WhelpImAGhost/LED20/Gantt Chart/LED20 Gantt Chart v3.pdf

29 | 6 | 13 | 20 | 27 | 3 | 10 | 17 | 24 | 1 | 8
9/24 | 10/24 | 11/24 | 12/24
ECE 411 - LED20 Practicum ... | 0h | 100%
Assignments | 0h | 100%
Class Survey | 0 | 100%
Resume | 0 | 100%
Form Practicum Teams | 0 | 100%
Set up Collab Site | 0 | 100%
Generate 3 Projects and Choose 1 | 0 | 100%
Product Design Specification (PDS) | 0 | 100%
Preliminary Schematic | 0 | 100%
Decision Matrix and AHP | 0 | 100%
Project Schedule | 0 | 100%
Updated Schematic | 0 | 100%
Preliminary PCB Layout | 0 | 100%
Breadboard Prototype | 0 | 100%
Rough Draft of CAD | 0 | 100%
Functional Decomposition | 0 | 100%
Bill of Materials | 0 | 100%
Design Review | 0 | 100%
Final CAD | 0 | 100%
Send Board to Fab | 0 | 100%
Sign up for Practicum Demo | 0 | 100%
Test Plan | 0 | 100%
Practicum Demo | 0 | 100%
Assignments Complete! | 0 | 100%
Phase 1 - Concept Generation | 0h | 100%
Brainstorm Project Ideas | 0 | 100%
Product Design Specification (PDS) | 0 | 100%
Preliminary Schematic | 0 | 100%
Concept Complete! | 0 | 100%
Phase 2 - Prototype Development | 0h | 100%
Updated Schematic | 0 | 100%
Preliminary PCB Layout | 0 | 100%
Preliminary 3D Model - D20 | 0 | 100%
Set up ESP32 | 0 | 100%
Test ESP32 | 0 | 100%
Set up Gyroscope | 0 | 100%
Test Gyroscope | 0 | 100%
Set up Accelerometer | 0 | 100%
Test Accelerometer | 0 | 100%
Set up LEDs | 0 | 100%
Test Complete Prototype | 0 | 100%
Discuss Wireless Charging Options | 0 | 100%
Settle on Wireless or USB Charging | 0 | 100%
Prototype Complete! | 0 | 100%
Phase 3 - MVP Development | 0h | 100%
Final BOM | 0 | 100%
Updated 3D Model - PCB and Battery... | 0 | 100%
Integrate Wireless Charging | 0 | 100%
Final CAD | 0 | 100%
Final 3D Model - D20 Halves Locking... | 0 | 100%
Fully Integrate Programming | 0 | 100%
Fully Integrate All Components | 0 | 100%
Send Board to Fab | 0 | 100%
MVP Complete! | 0 | 100%
Phase 4 - Final Testing and Delivery | 0h | 100%
Pick up Board from EPL | 0 | 100%
Test Board | 0 | 100%
Write Presentation Slides | 0 | 100%
Practice Presentation and Demo | 0 | 100%
Present | 0 | 100%
Project Complete! | 0 | 100%

Brad Glaubitz, Caleb Monti, Chris Kane-Pardy, Henry Sanders
Brad Glaubitz, Caleb Monti, Chris Kane-Pardy, Henry Sanders Brad Glaubitz, Caleb Monti, Chris Kane-Pardy, Henry Sanders Caleb Monti
Chris Kane-Pardy, Henry Sanders
Brad Glaubitz, Caleb Monti, Chris Kane-Pardy, Henry Sanders Brad Glaubitz, Henry Sanders
Henry Sanders
Henry Sanders
Brad Glaubitz, Henry Sanders
Brad Glaubitz, Caleb Monti, Chris Kane-Pardy, Henry Sanders Caleb Monti, Chris Kane-Pardy
Brad Glaubitz, Caleb Monti, Chris Kane-Pardy, Henry Sanders Caleb Monti, Henry Sanders Brad Glaubitz
Brad Glaubitz, Caleb Monti, Chris Kane-Pardy, Henry Sanders
Brad Glaubitz, Caleb Monti, Chris Kane-Pardy, Henry Sanders
Brad Glaubitz, Caleb Monti, Chris Kane-Pardy, Henry Sanders Brad Glaubitz, Caleb Monti, Chris Kane-Pardy, Henry Sanders
Brad Glaubitz, Caleb Monti, Chris Kane-Pardy, Henry Sanders Brad Glaubitz, Caleb Monti, Chris Kane-Pardy, Henry Sanders

Brad Glaubitz, Caleb Monti, Chris Kane-Pardy, Henry Sanders
Brad Glaubitz, Caleb Monti, Chris Kane-Pardy, Henry Sanders Brad Glaubitz, Henry Sanders

Brad Glaubitz, Henry Sanders
Brad Glaubitz, Caleb Monti, Chris Kane-Pardy, Henry Sanders Chris Kane-Pardy
Caleb Monti
Caleb Monti
Caleb Monti
Caleb Monti
Caleb Monti
Caleb Monti
Caleb Monti
Brad Glaubitz, Caleb Monti, Chris Kane-Pardy, Henry Sanders Brad Glaubitz, Henry Sanders
Brad Glaubitz, Henry Sanders

Brad Glaubitz, Chris Kane-Pardy Chris Kane-Pardy
Brad Glaubitz, Henry Sanders
Brad Glaubitz, Caleb Monti, Chris Kane-Pardy, Henry Sanders Chris Kane-Pardy
Caleb Monti, Chris Kane-Pardy Brad Glaubitz, Chris Kane-Pardy, Henry Sanders Brad Glaubitz, Caleb Monti, Chris Kane-Pardy, Henry Sanders

Caleb Monti
Brad Glaubitz, Caleb Monti, Chris Kane-Pardy, Henry Sanders
Brad Glaubitz, Caleb Monti, Chris Kane-Pardy, Henry Sanders
Brad Glaubitz, Caleb Monti, Chris Kane-Pardy, Henry Sanders Brad Glaubitz, Caleb Monti, Chris Kane-Pardy, Henry Sanders

Powered by TCPDF (www.tcpdf.org)
