WhelpImAGhost/LED20/Functional Decomposition/Functional Decomposition.pdf

Caleb Monti
Brad Glaubitz
Henry Sanders
Chris Kane-Pardy
14 November 2024

## LED 20: Functional Decomposition

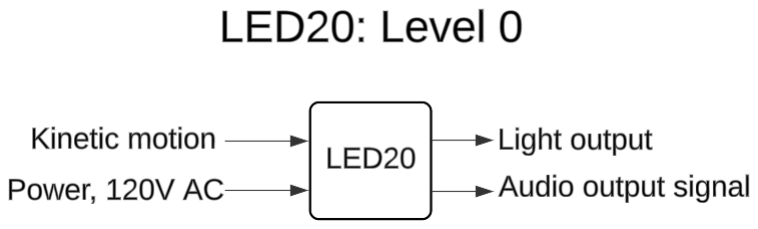
[picture p8: figure]

Module | LED20
Inputs | Kinetic motion: Significant motion detection Power: 120V AC rms, 60 Hz
Outputs | Light output: LEDs Audio output signal: Buzzer
Functionality | The device is interrupted via a significant motion from the user, producing light and audio outputs.

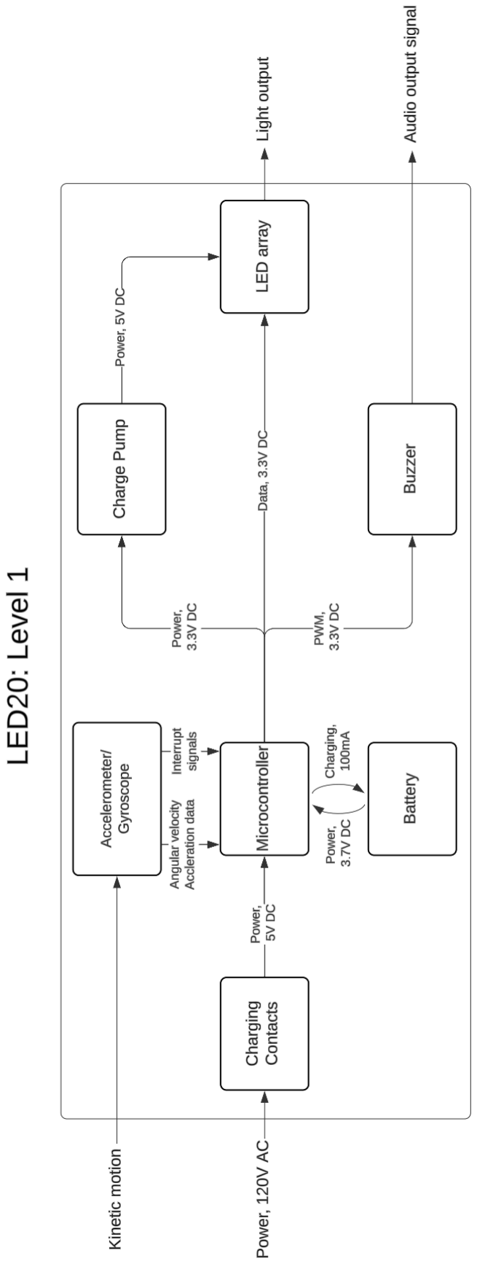
[picture p9: figure]

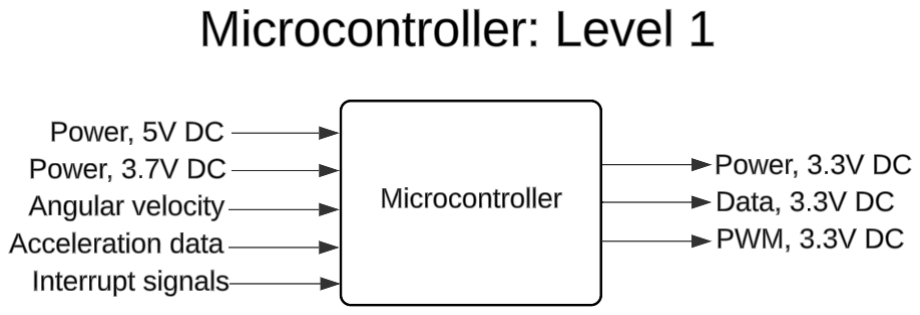
[picture p10: figure]

Module | Microcontroller
Inputs | Power: 5V DC from Charging Contacts Power: 3.7V DC from Battery Angular velocity: (-500, 500) degrees per second (DPS) Acceleration data: (0-4) g (acceleration due to gravity 2 g = 9. 81m/s ) Interrupt signals: to Accelerometer/Gyroscope
Outputs | Power: 3.3V DC to Charge Pump Data: 3.3V DC to LED array PWM: 3.3V DC to Buzzer
Functionality | Receives 5V DC from Charging Contacts for charging the battery, 3.7V DC from the battery to power self, angular velocity and acceleration data from Accelerometer/Gyroscope for determining when the device is in motion, no longer in motion, and at what orientation, and interrupt signals to Accelerometer/Gyroscope for both waking device up and putting to sleep after a period of unuse. Outputs 3.3V DC to charge pump, 3.3V data signal to LED Array based on angular velocity and acceleration data, and 3.3V PWM signal to Buzzer based on the orientation of the device.

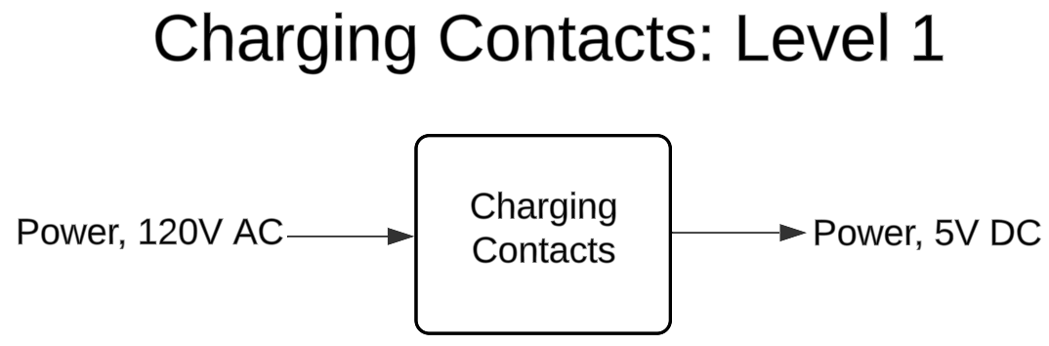
[picture p11: figure]

Module | Charging Contacts
Inputs | Power: 120V AC rms, 60 Hz
Outputs | Power: 5V DC
Functionality | Provide wireless charging via conductive contacts

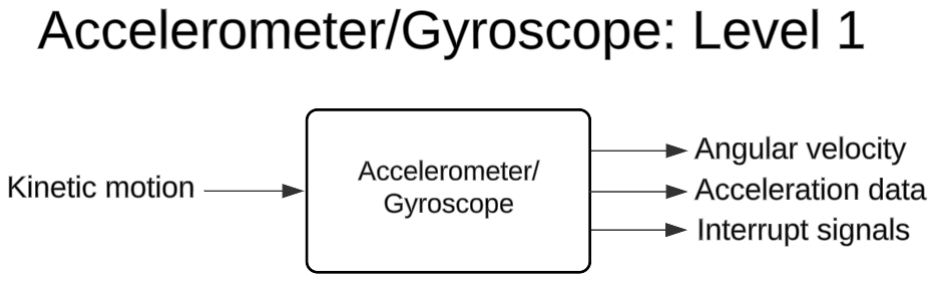
[picture p12: figure]

Module | Accelerometer/Gyroscope
Inputs | Kinetic motion: Significant motion detection
Outputs | Angular velocity: (-500, 500) dps Acceleration data: (0-4) g Interrupt signals: to Microcontroller
Functionality | Detects significant motion from the user, relays angular velocity and acceleration data to the Microcontroller, interrupt signals to both wake up and put the Accelerometer/Gyroscope to sleep.

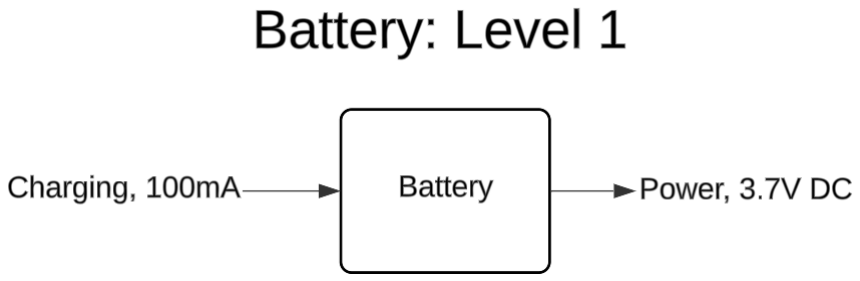
[picture p13: figure]

Module | Battery
Inputs | Charging: 100mA, limited by Microcontroller
Outputs | Power: 3.7V DC
Functionality | 500mAh LiPo battery, supplies 3.7V DC to Microcontroller

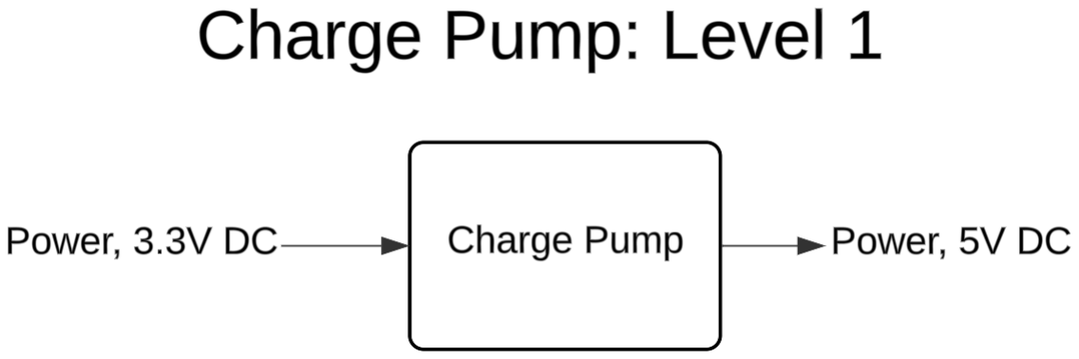
[picture p14: figure]

Module | Charge Pump
Inputs | Power: 3.3V DC from Microcontroller
Outputs | Power: 5V DC, 250mA max
Functionality | Converts 3.3V input from Microcontroller to 5V output to power LED Array

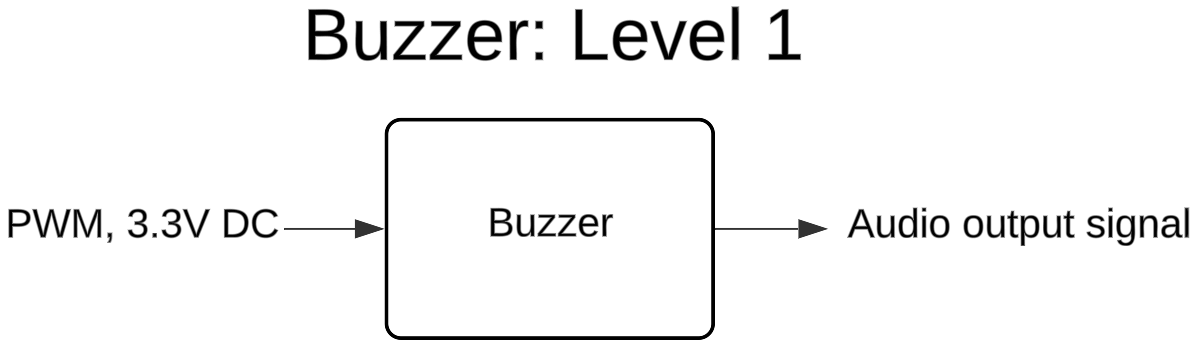
[picture p15: figure]

Module | Buzzer
Inputs | PWM: 3.3V DC
Outputs | Audio output signal: celebratory or disheartening tune
Functionality | Receives 3.3V PWM signal from microcontroller when particular values are read from accelerometer/gyroscope, emits tune based on the read value

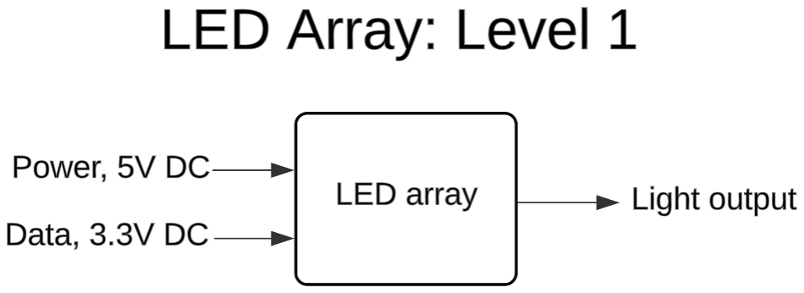
[picture p16: figure]

Module | LED Array
Inputs | Power: 5V DC from charge pump Data: 3.3V DC signal from microcontroller
Outputs | Light output: LEDs
Functionality | Illuminates particular LED in the array based on the orientation of the device determined by the accelerometer/gyroscope module
