WhelpImAGhost/LED20/CAD/Schematics and PCB Layouts/PDFs/Schematic/Updated Schematic 11-4-24/led20_updated_schematic_11_4_24.pdf

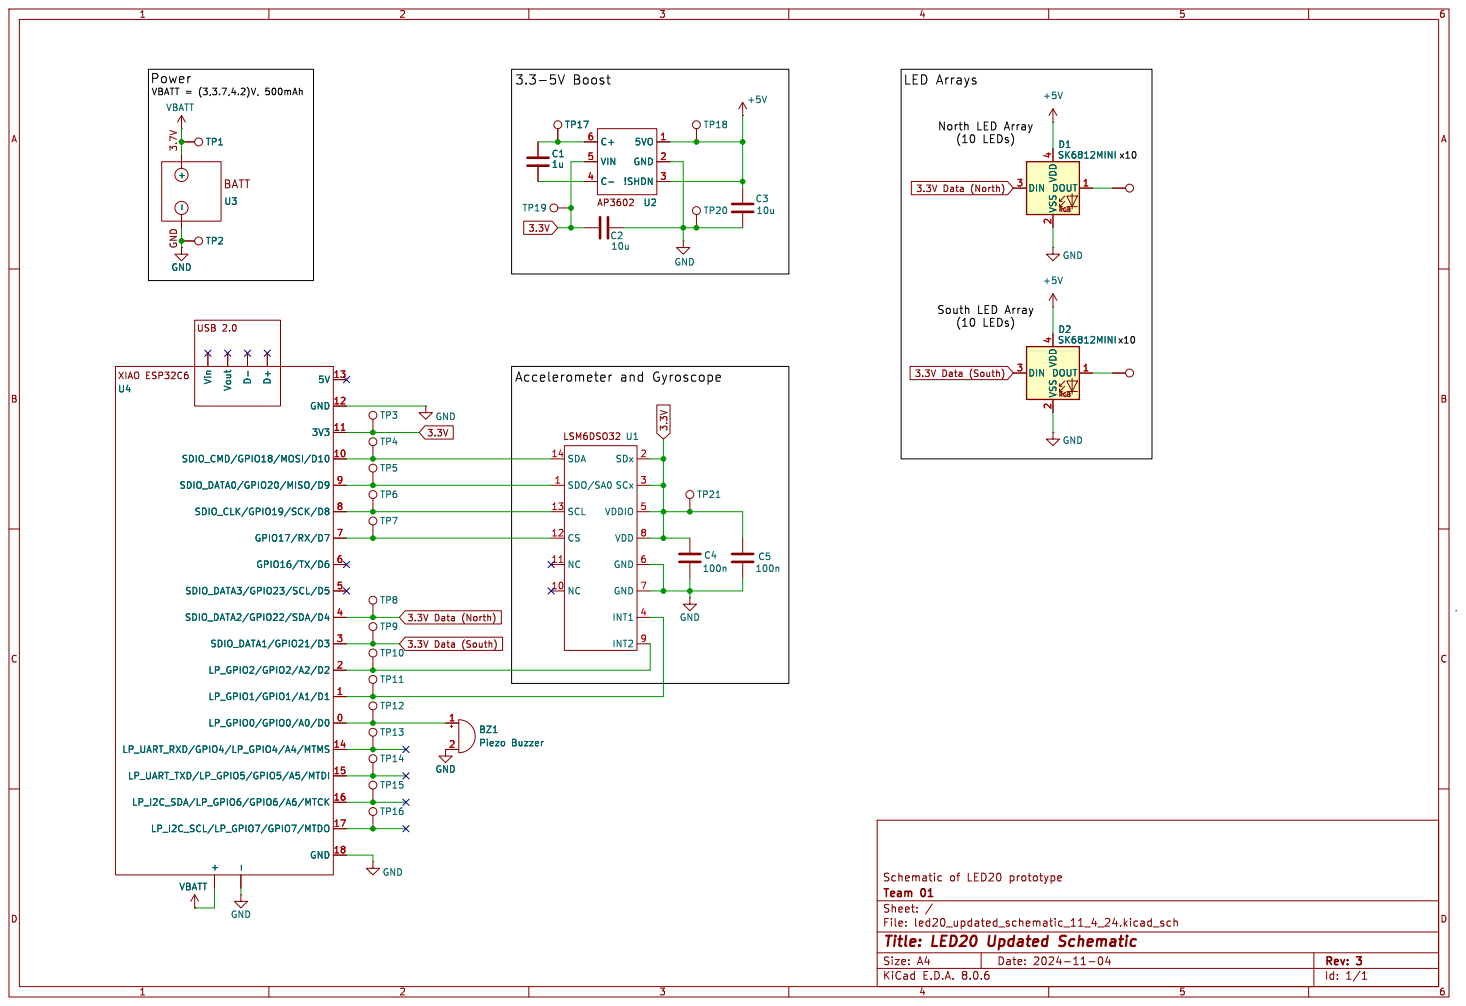
[picture p31: page 1]

x10 LED Arrays
(10 LEDs) North LED Array

3.3V Data (South)

Id: 1/1 Title: LED20 Updated Schematic
