WhelpImAGhost/LED20/CAD/Schematics and PCB Layouts/PDFs/Schematic/Updated Schematic 10-31-24/led20_updated_schematic_10_31_24.pdf

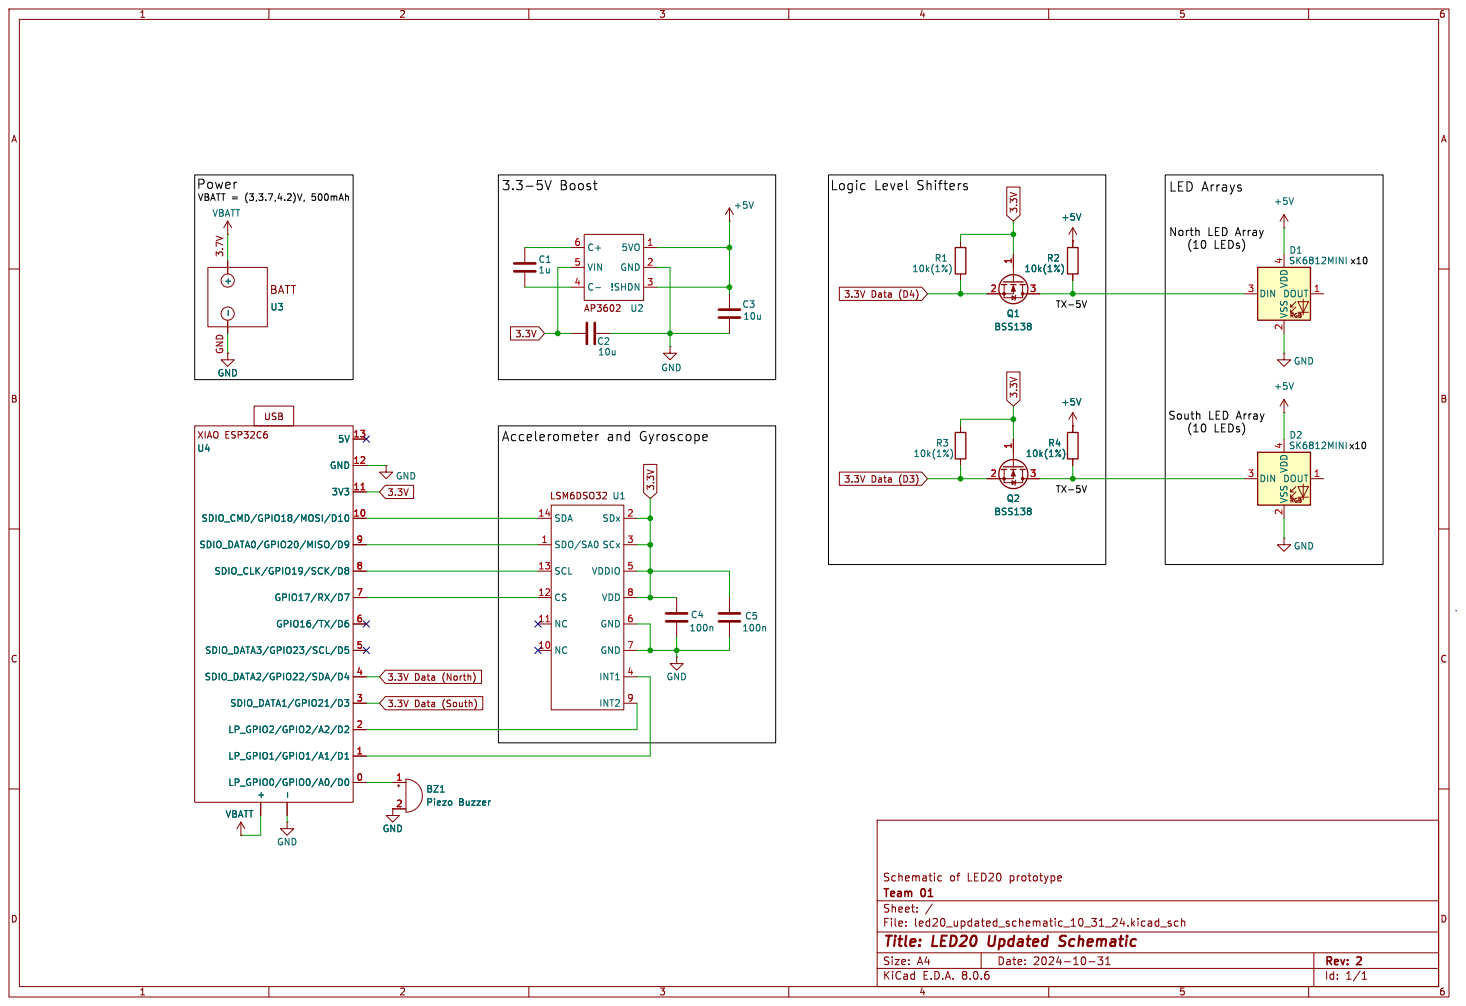
[picture p32: page 1]

LED Arrays North LED Array

3.3V Data (D4) 3.3V Data (South) 3.3V Data (North)

Id: 1/1 Title: LED20 Updated Schematic
