WhelpImAGhost/LED20/CAD/Schematics and PCB Layouts/PDFs/PCB/Rough Draft PCB Layout/Single PCB Layouts/led20_PCB_Layout_Front_Back.pdf

Id: 1/1 Title: LED20 Updated Schematic
