WhelpImAGhost/LED20/Functional Decomposition/UML.pdf

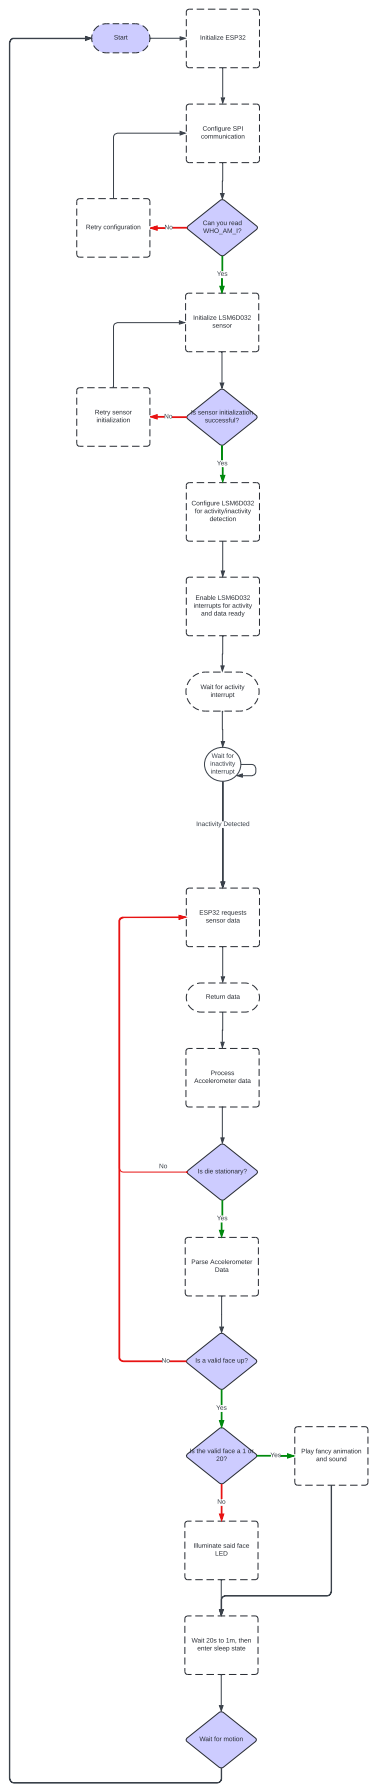
[picture p33: page 1]
Start; Initialize ESP32; Configure SPI communication; WHO_AM_I? No; Initialize LSM6D032 sensor; ESP32 requests sensor data; Return data; Yes; Retry configuration; Retry sensor initialization; Inactivity Detected; Parse Accelerometer Data; Process Accelerometer data; Wait for inactivity interrupt

Can you read

Is sensor initialization
successful?

Configure LSM6D032
for activity/inactivity
detection

Enable LSM6D032
interrupts for activity
and data ready

Wait for activity
interrupt

Is die stationary?

Is a valid face up?

Is the valid face a 1 or

Play fancy animation
and sound

Illuminate said face
LED

Wait 20s to 1m, then
enter sleep state

Wait for motion
