WhelpImAGhost/LED20/Functional Decomposition/LED20 L0 and L1.pdf

# LED20: Level 1

# LED20: Level 0

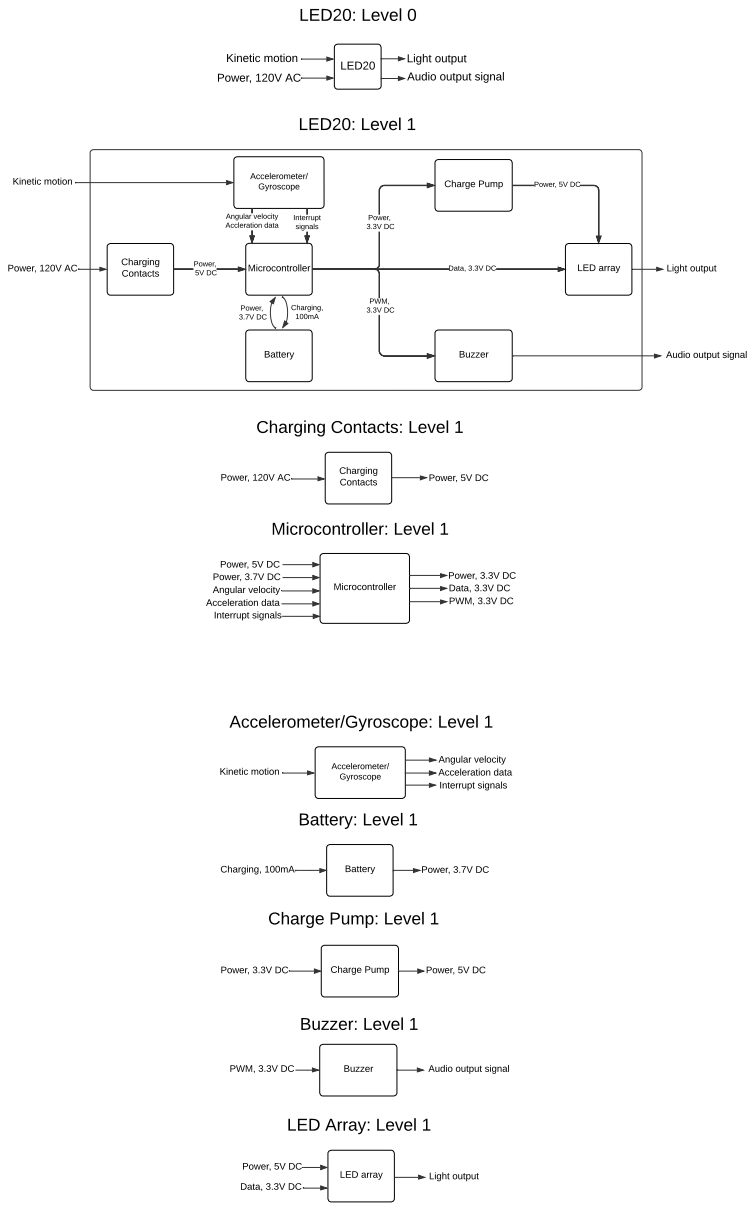
[picture p34: page 1]
LED20; Microcontroller; Accelerometer/ Gyroscope; Battery; Charging, 100mA; Power, 3.7V DC; Charge Pump; Power, 3.3V DC; Data, 3.3V DC; Power, 5V DC; Buzzer; PWM, 3.3V DC; Kinetic motion Power, 120V AC; Kinetic motion; Light output; LED array; Charging Contacts; Power,; Microcontroller: Level 1; Battery: Level 1; Buzzer: Level 1; Audio output signal; Power, 120V AC; Angular velocity Acceleration data; Power, 3.3V DC Data, 3.3V DC PWM, 3.3V DC; Power, 5V DC Power, 3.7V DC; Interrupt signals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

Light output
Audio output signal

5V DC Power, 120V AC

Charging Contacts: Level 1

Accelerometer/Gyroscope: Level 1

Charge Pump: Level 1

LED Array: Level 1
